JaJenks2/ECE445-Oscillosketch/Oscillosketch/audio_stream.h

#pragma once
#include <Arduino.h>

struct AudioStreamStats {
  uint32_t packetsAccepted;
  uint32_t duplicatePackets;
  uint32_t sequenceErrors;
  uint32_t missingPackets;
  uint32_t crcErrors;
  uint32_t parserResets;
  uint32_t bufferOverwrites;
  uint32_t underruns;
  size_t currentFill;
  size_t maxFill;
  uint16_t expectedSeq;
  bool sessionStarted;
  bool active;
};

void audioStreamBegin();
void audioStreamReset();
void audioStreamPollSerial();

size_t audioStreamAvailableFrames();
bool audioStreamPopFrame(int16_t& left, int16_t& right);
bool audioStreamIsActive();

void audioStreamGetStats(AudioStreamStats& out);
